TannerNelson16/morse_code_optical_receiver/photodetector_circuit.asc

C1: cap; 50p
C2: cap; 47n
C3: cap; 220p
I1: current; PULSE(0 70u 0 1m 1m 500m 1 100)
R1: res; 47k
R2: res; 1k
R3: res; 1Meg
R4: res; 300
R5: res; 30k
R6: res; 1k
R7: res; 1Meg
U1: lm358
U2: lm358
V1: voltage; 5
V2: voltage; 3.3V
Named nets: VCC, 0, 3.3REF
.tran 5
